Acliad/Power-Supply-V3/PCB Files/Board Layout.png

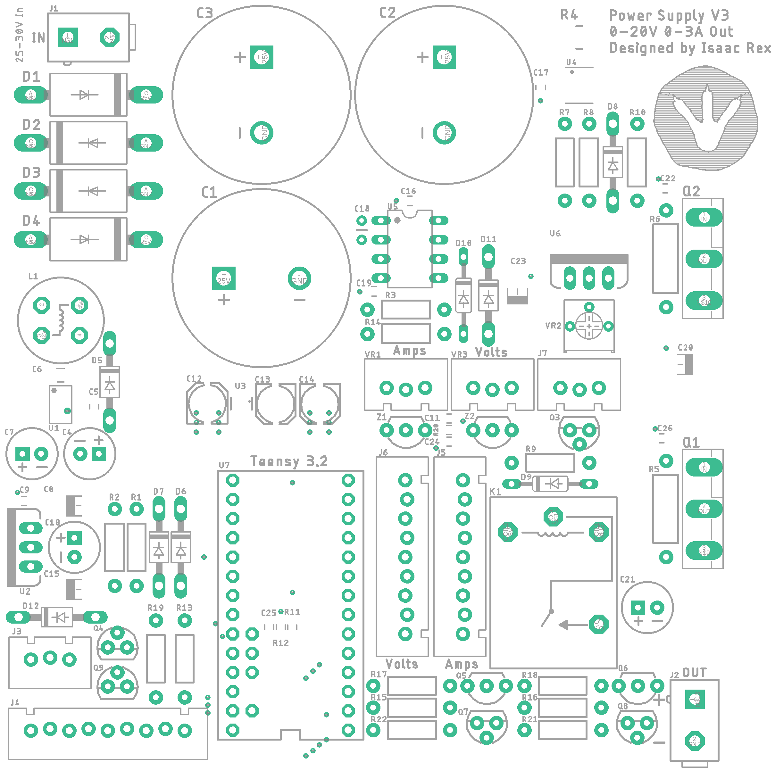
PCB Files/Board Layout.png
