Acliad/Power-Supply-V3/PCB Files/Power Supply 2:2.png

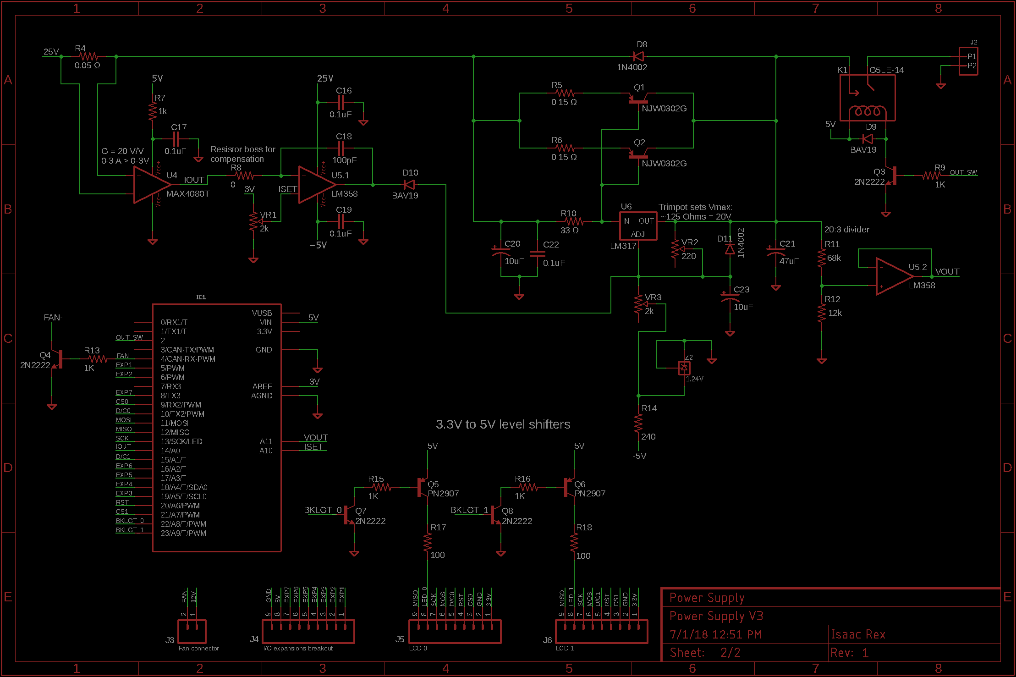
PCB Files/Power Supply 2:2.png
