Acliad/Power-Supply-V3/Software/step_response.png

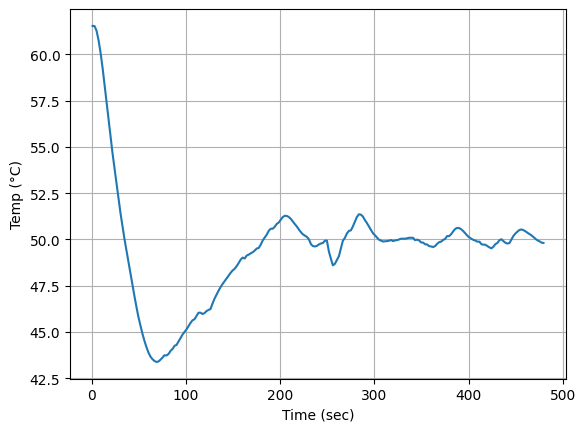
Software/step_response.png
